sichzp/ClimaticDisplay/CAD/BOTTOM.bmp

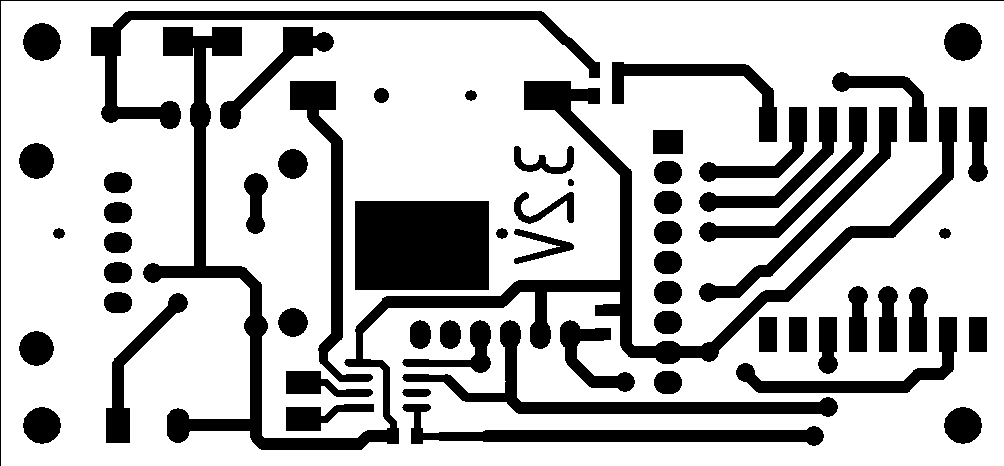
CAD/BOTTOM.bmp
