sichzp/ClimaticDisplay/CAD/TOP.bmp

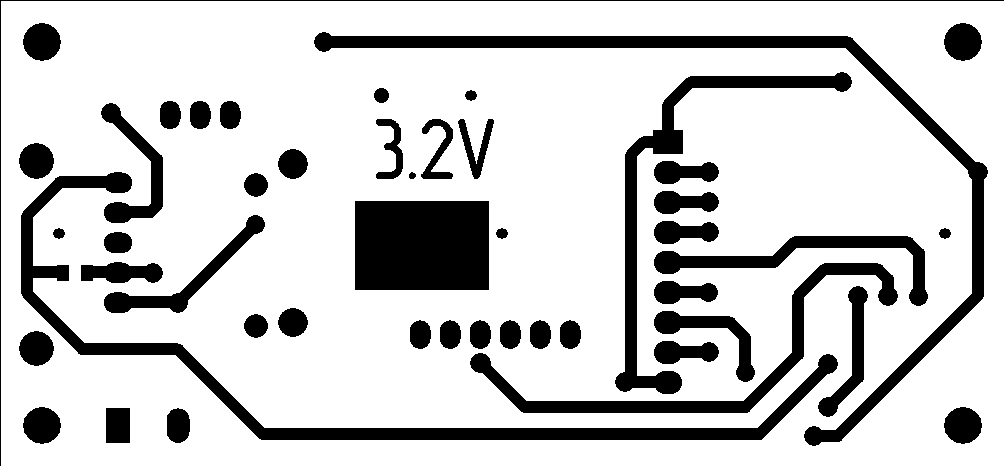
CAD/TOP.bmp
