sichzp/ClimaticDisplay/DOC/ESP32_C3.png

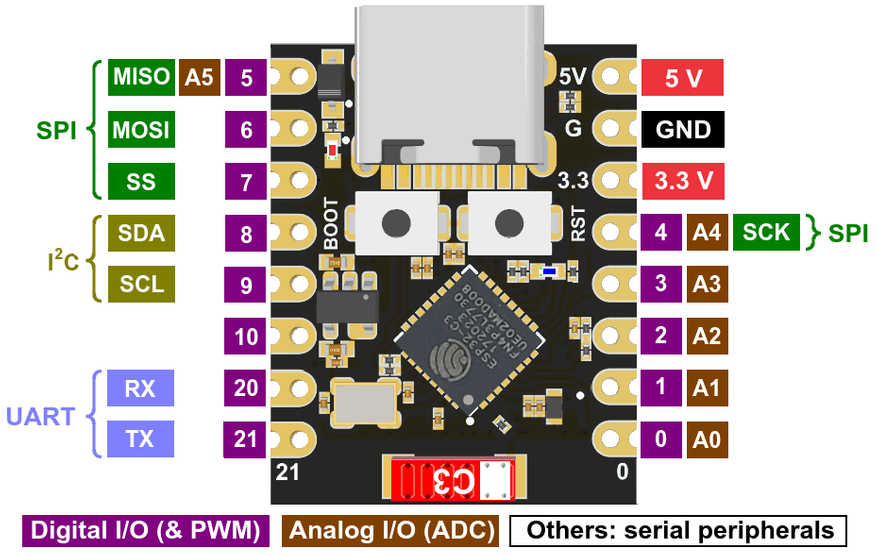
DOC/ESP32_C3.png
