sichzp/ClimaticDisplay/DOC/Настройки программы Img2Lcd.PNG

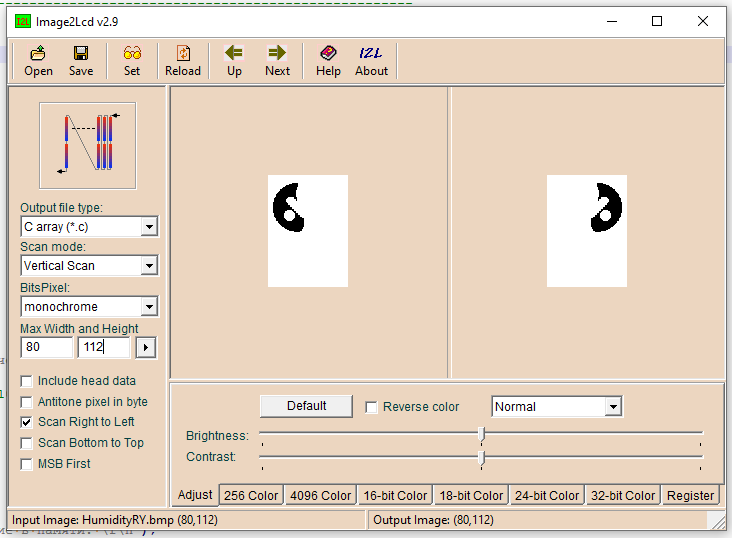
DOC/Настройки программы Img2Lcd.PNG
