sichzp/ClimaticDisplay/Img/MainWindow.png

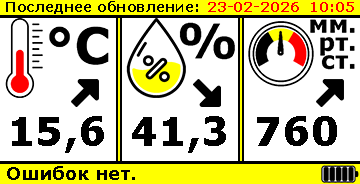
Img/MainWindow.png
